mitTheos/KLORTHEOS/case/Alternate Case Design/Tenting Legs/images/choc-sofle-2.jpg

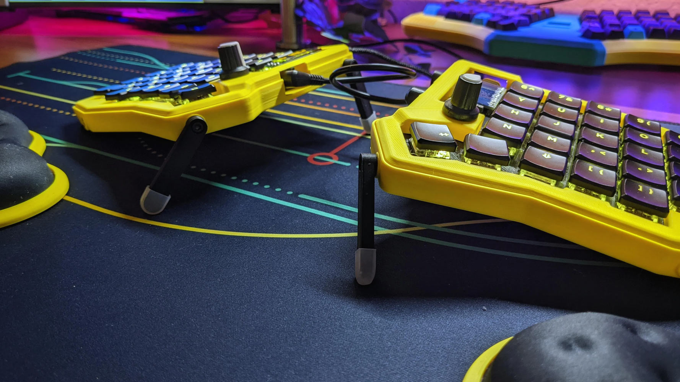
case/Alternate Case Design/Tenting Legs/images/choc-sofle-2.jpg
