mitTheos/KLORTHEOS/case/Alternate Case Design/Tenting Legs/images/tentingLeg26mm.png

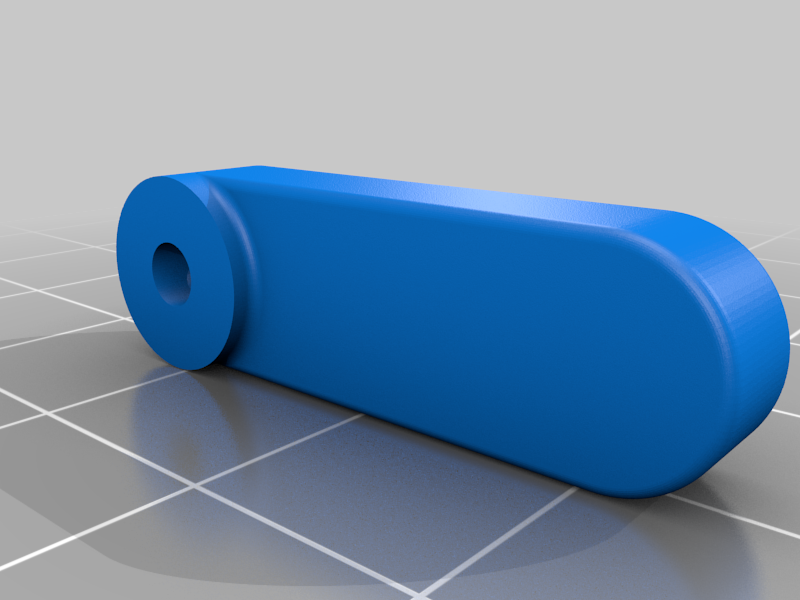
case/Alternate Case Design/Tenting Legs/images/tentingLeg26mm.png
