mitTheos/KLORTHEOS/case/Alternate Case Design/Tenting Legs/images/tentingleg36mm.png

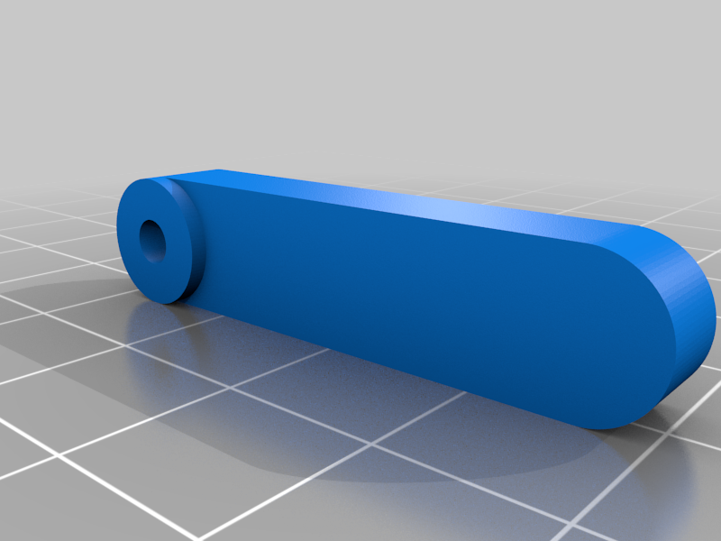
case/Alternate Case Design/Tenting Legs/images/tentingleg36mm.png
