mitTheos/KLORTHEOS/case/Alternate Case Design/Tenting Legs/images/tentingLegALT31mm.png

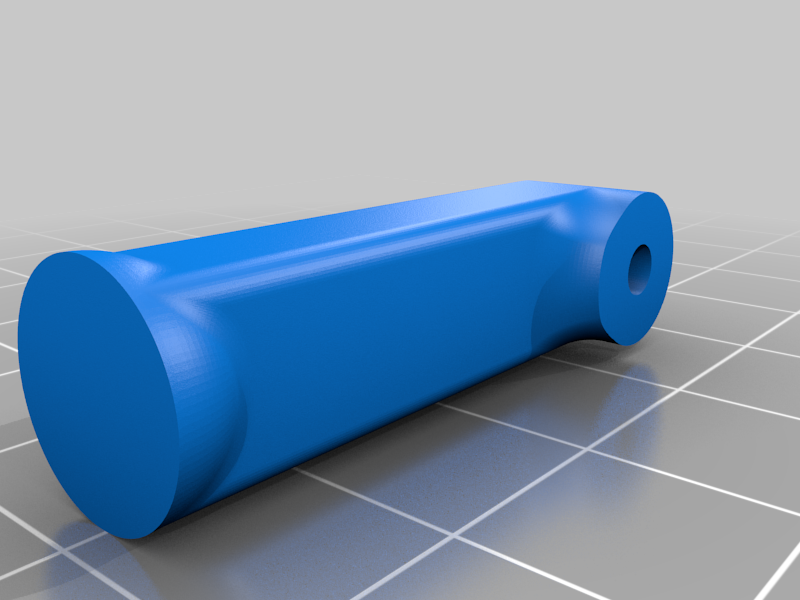
case/Alternate Case Design/Tenting Legs/images/tentingLegALT31mm.png
