mitTheos/KLORTHEOS/case/Alternate Case Design/Tenting Legs/images/tentingLegALT37mm.png

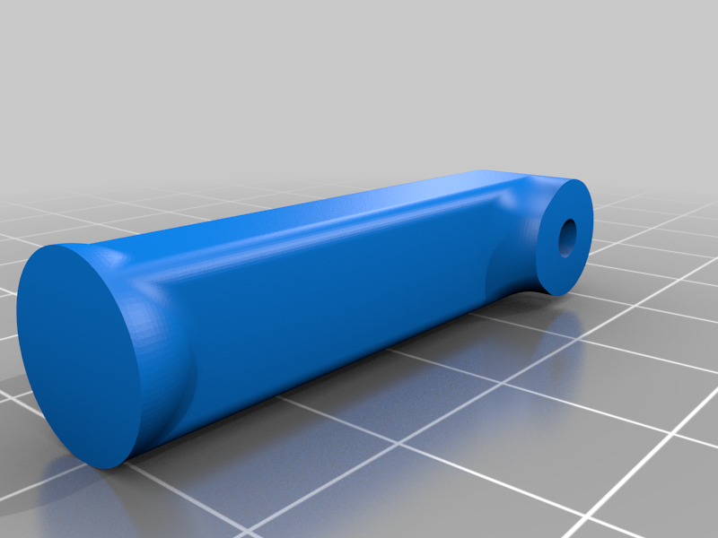
case/Alternate Case Design/Tenting Legs/images/tentingLegALT37mm.png
