mitTheos/KLORTHEOS/case/docs/images/konrad_3dp.png

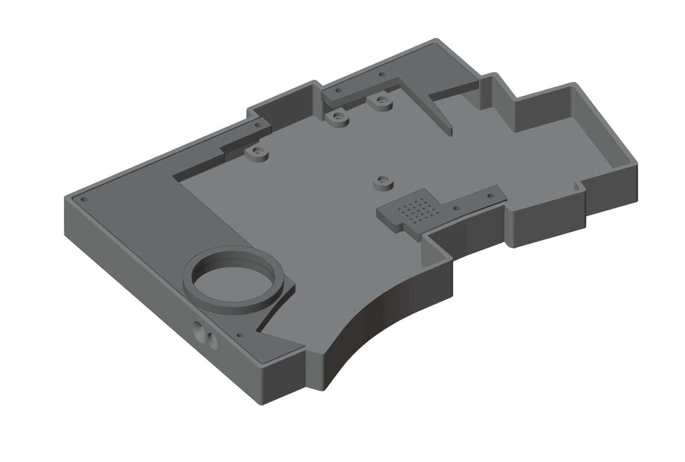
case/docs/images/konrad_3dp.png
