mitTheos/KLORTHEOS/case/docs/images/konrad_acryl.png

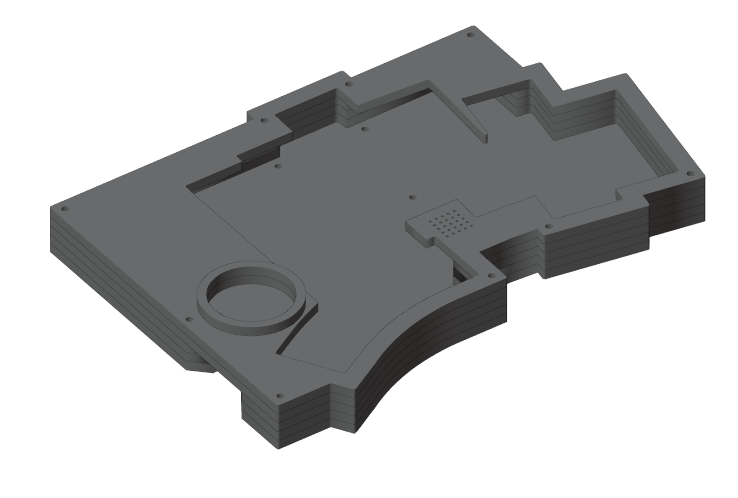
case/docs/images/konrad_acryl.png
