mitTheos/KLORTHEOS/case/docs/images/saegewerk_3dp_ble_puck.png

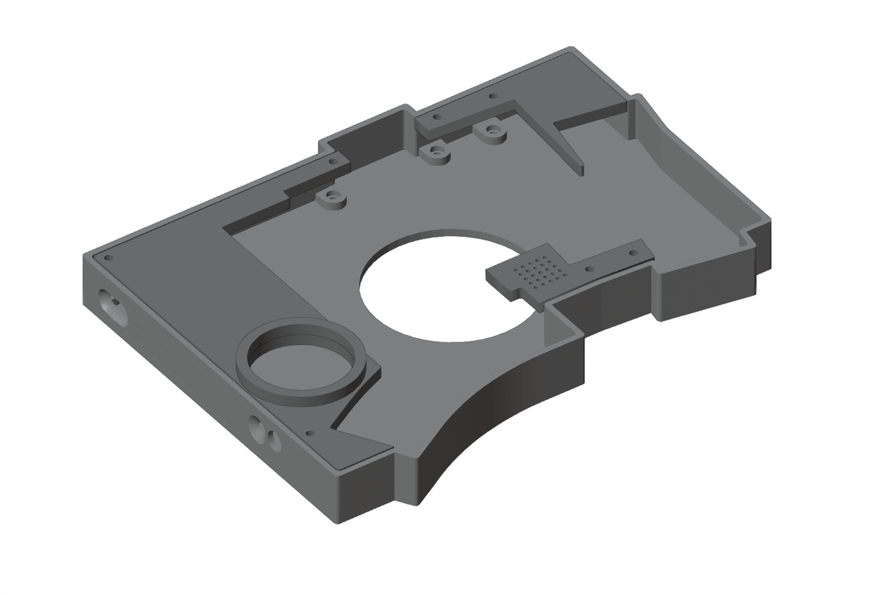
case/docs/images/saegewerk_3dp_ble_puck.png
