mitTheos/KLORTHEOS/docs/images/Klor_1.4_picture7.png

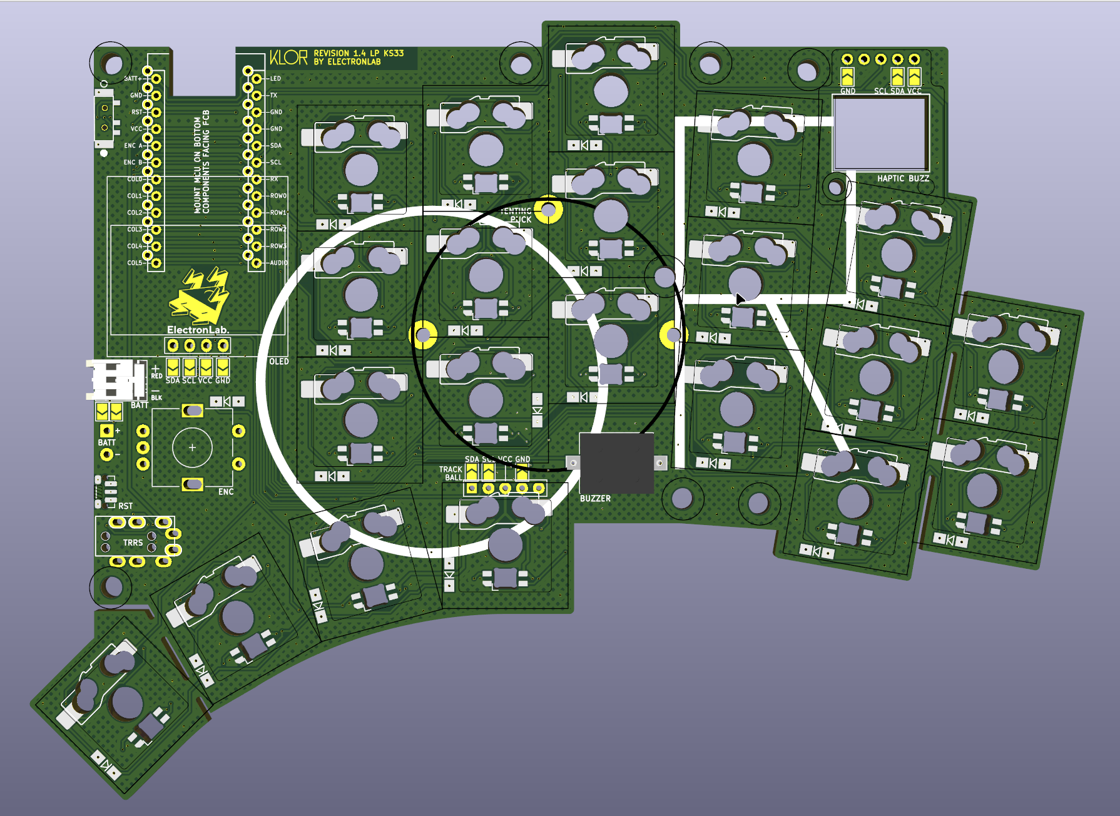
docs/images/Klor_1.4_picture7.png
