mitTheos/KLORTHEOS/docs/images/KLOR_1.5.png

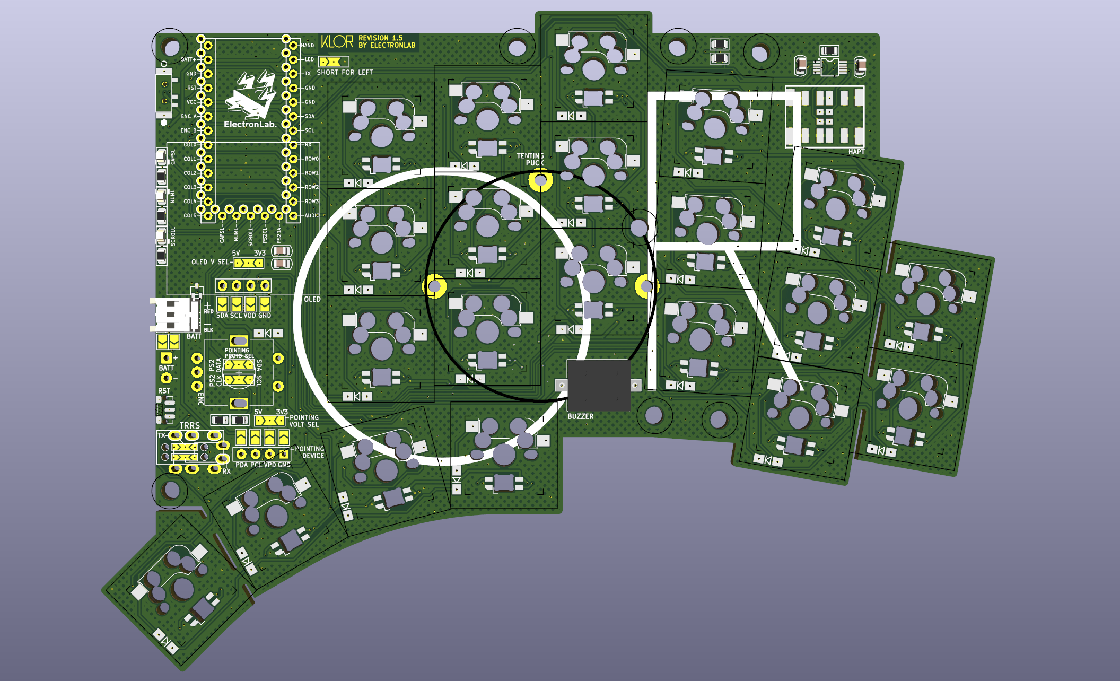
docs/images/KLOR_1.5.png
