mitTheos/KLORTHEOS/docs/images/KLOR_knob1-2.png

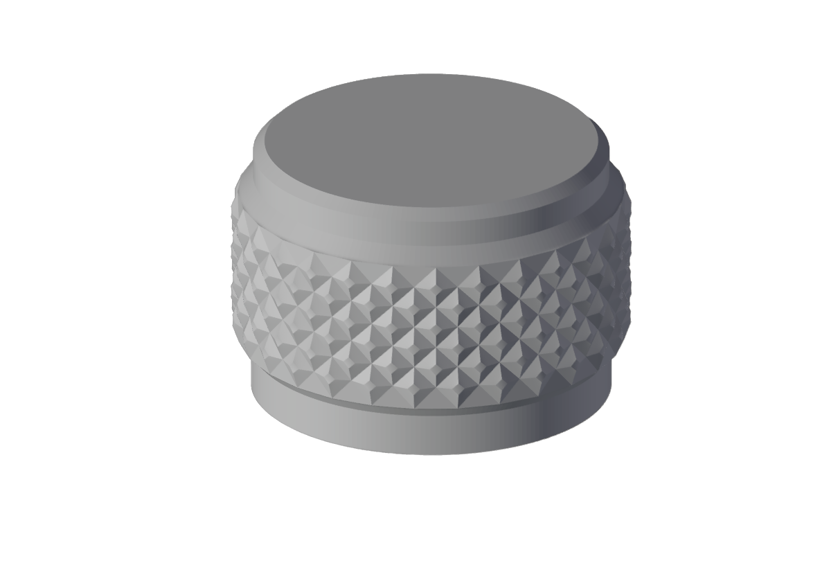
docs/images/KLOR_knob1-2.png
