mitTheos/KLORTHEOS/docs/images/KLOR_knob_resin_nylon.jpg

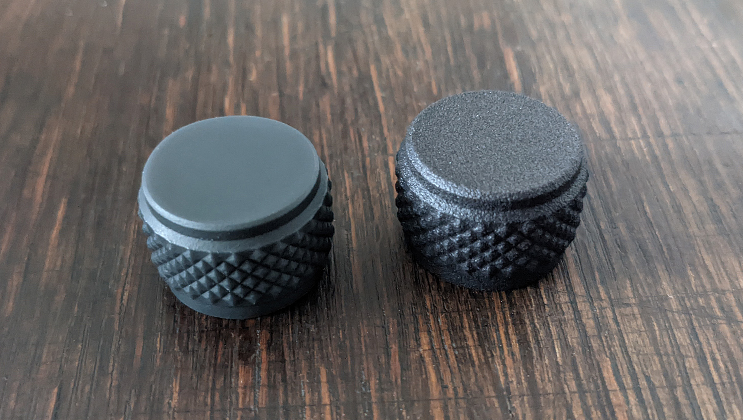
docs/images/KLOR_knob_resin_nylon.jpg
