mitTheos/KLORTHEOS/docs/images/KLOR_polydactyl_DES01.jpg

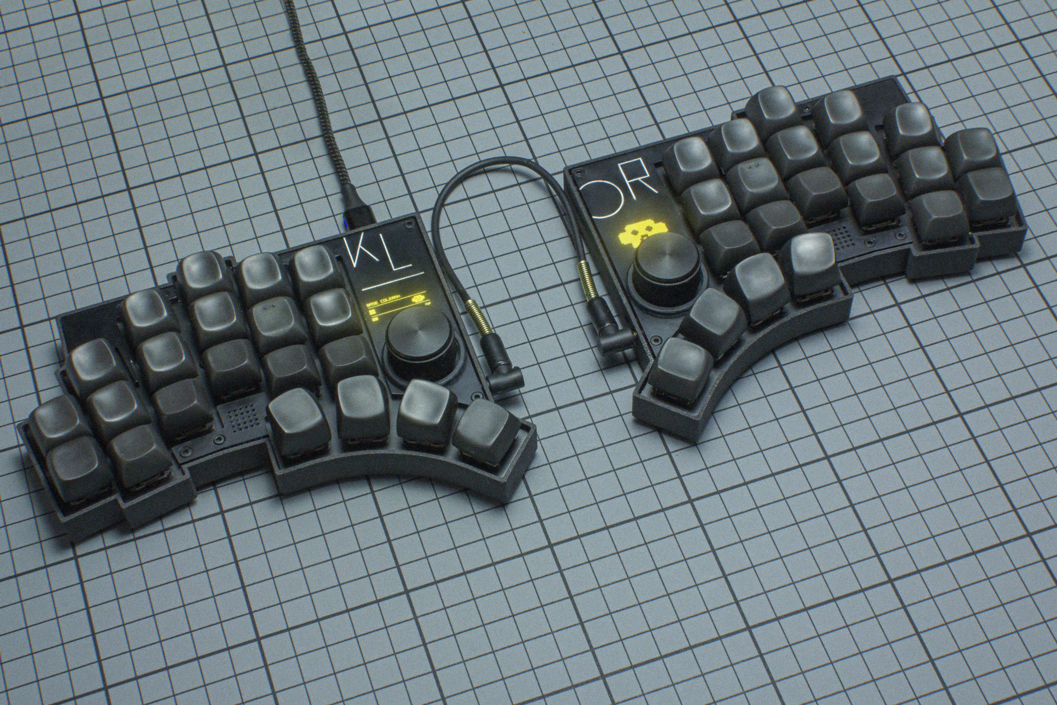
docs/images/KLOR_polydactyl_DES01.jpg
