mitTheos/KLORTHEOS/docs/images/KLOR_polydactyl_DES02.jpg

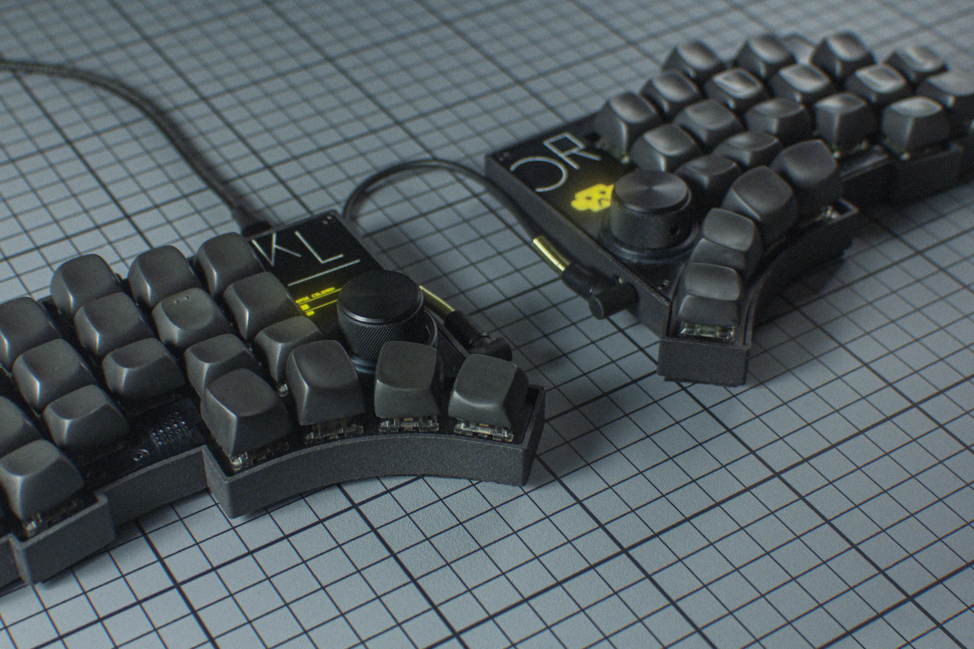
docs/images/KLOR_polydactyl_DES02.jpg
