mitTheos/KLORTHEOS/docs/images/KLOR_saegewerk_GRID01.jpg

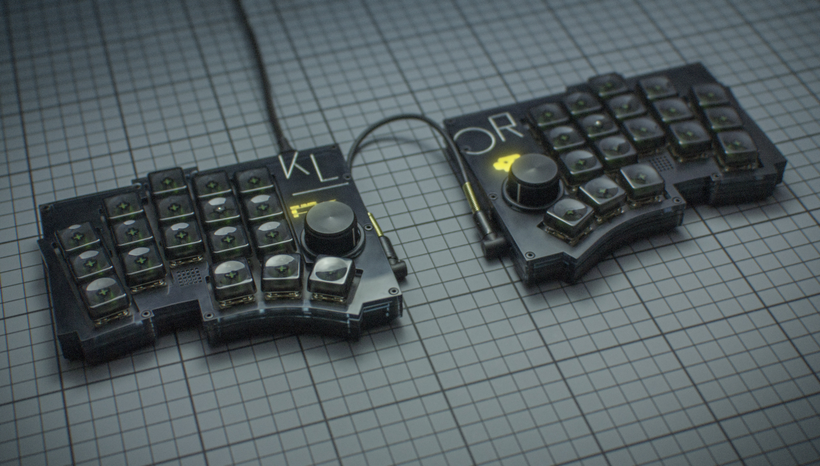
docs/images/KLOR_saegewerk_GRID01.jpg
