mitTheos/KLORTHEOS/docs/images/KLOR_saegewerk_GRID02.jpg

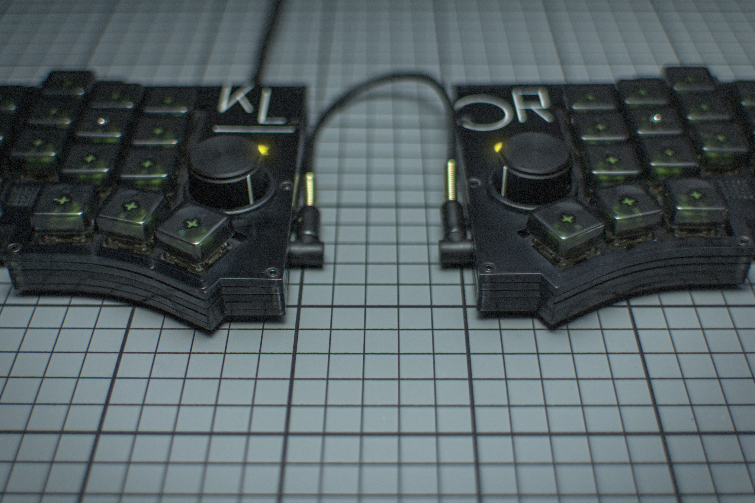
docs/images/KLOR_saegewerk_GRID02.jpg
