mitTheos/KLORTHEOS/docs/images/KLORpcb.png

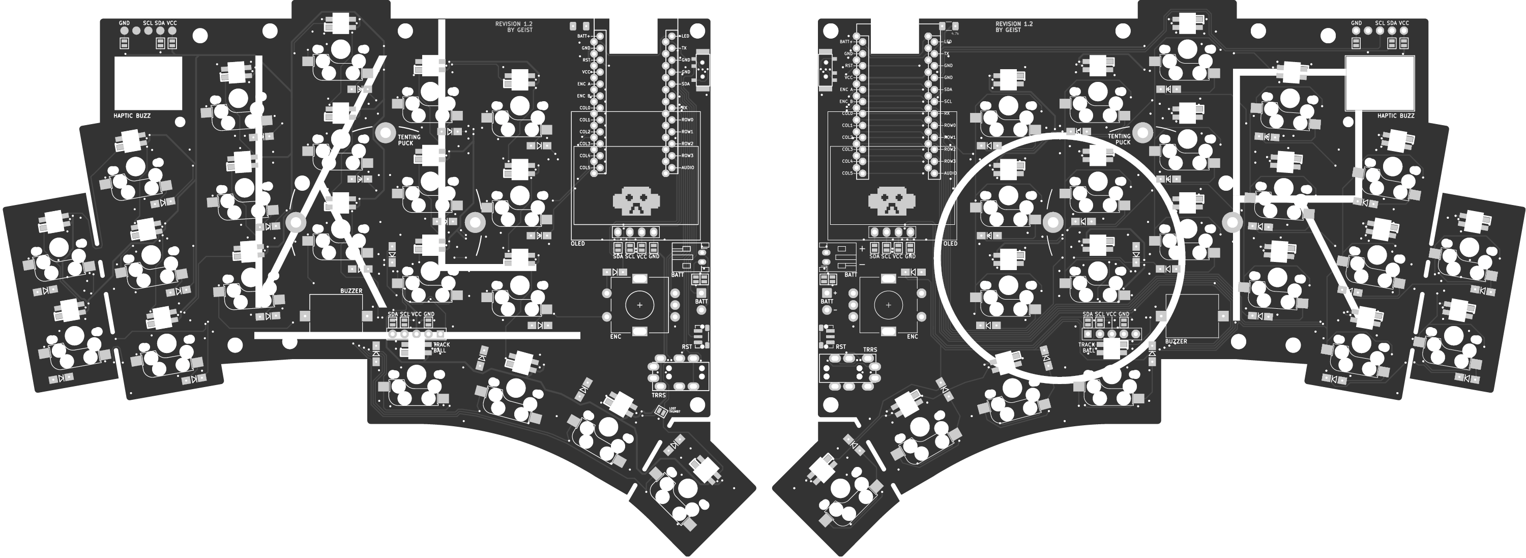
docs/images/KLORpcb.png
