mitTheos/KLORTHEOS/docs/images/KLORpinout.png

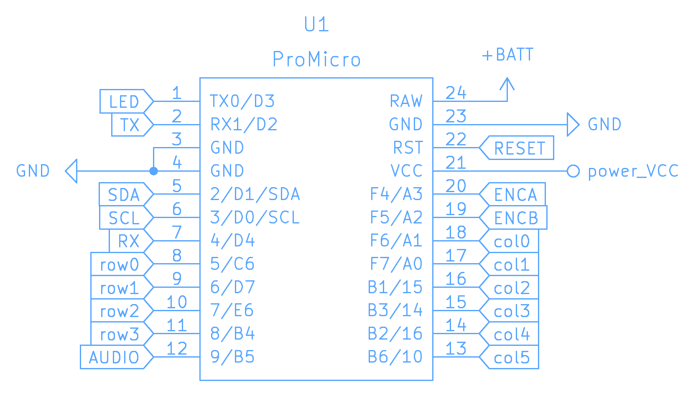
docs/images/KLORpinout.png
