mitTheos/KLORTHEOS/docs/images/KLORtraces.png

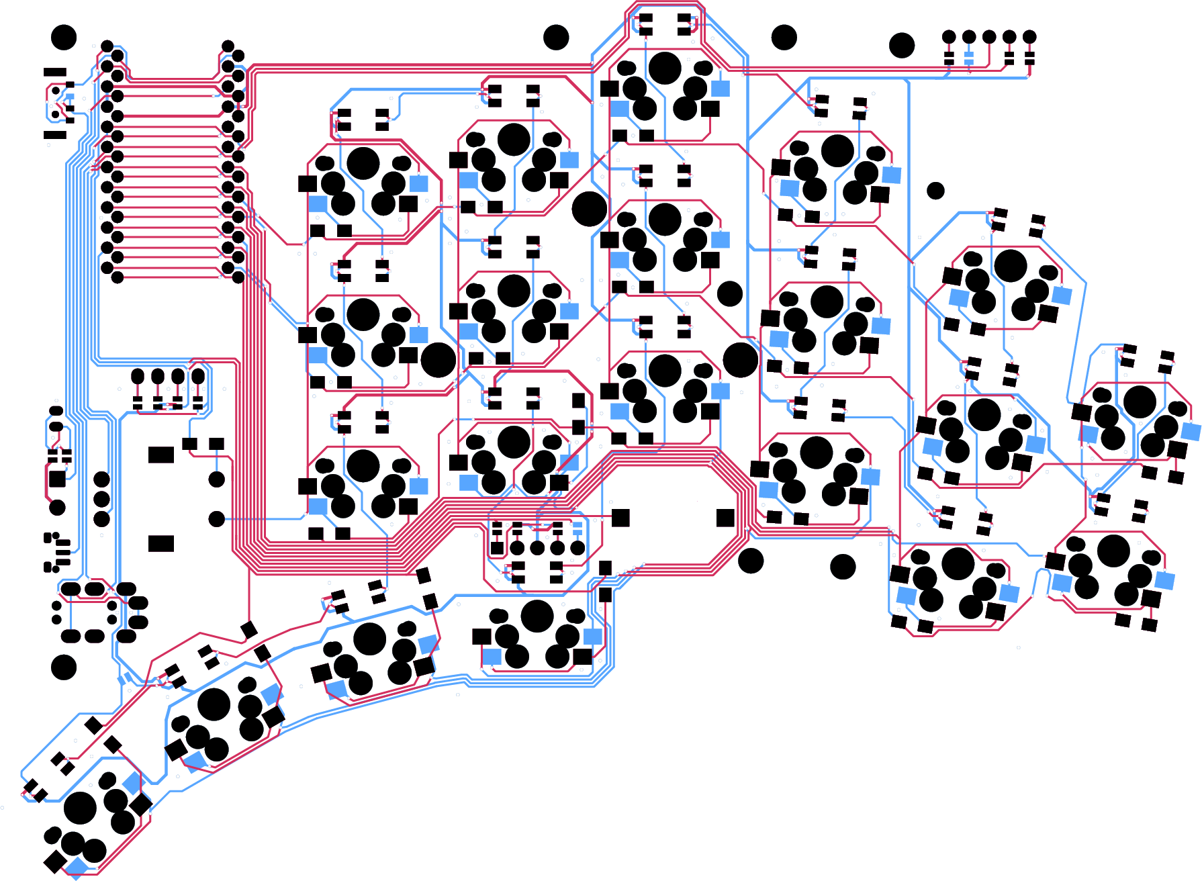
docs/images/KLORtraces.png
