mitTheos/KLORTHEOS/case/Alternate Case Design/EncoderInsert-flat-16mm.stl

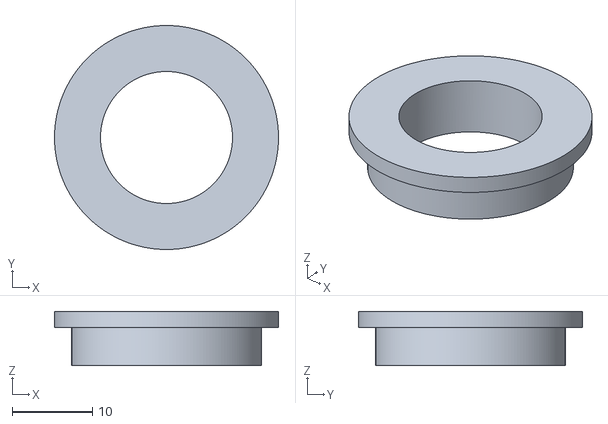
[picture p50: CAD file, 2024-07-25]
case/Alternate Case Design/EncoderInsert-flat-16mm.stl
28.0 x 28.0 x 6.80
