mitTheos/KLORTHEOS/case/Alternate Case Design/Konrad/SwitchPlate-Konrad.stl

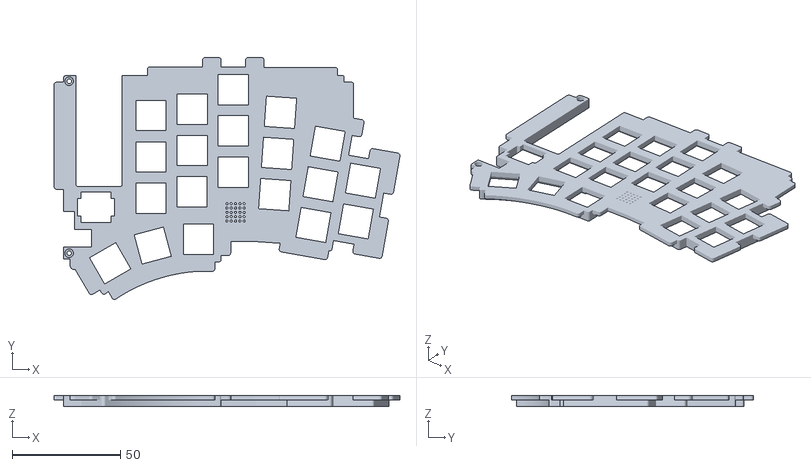
[picture p51: CAD file, 2024-07-25]
case/Alternate Case Design/Konrad/SwitchPlate-Konrad.stl
159.8 x 111.8 x 5.00
