mitTheos/KLORTHEOS/case/Alternate Case Design/Polydactyl/v2-GasketSwitchPlate.stl

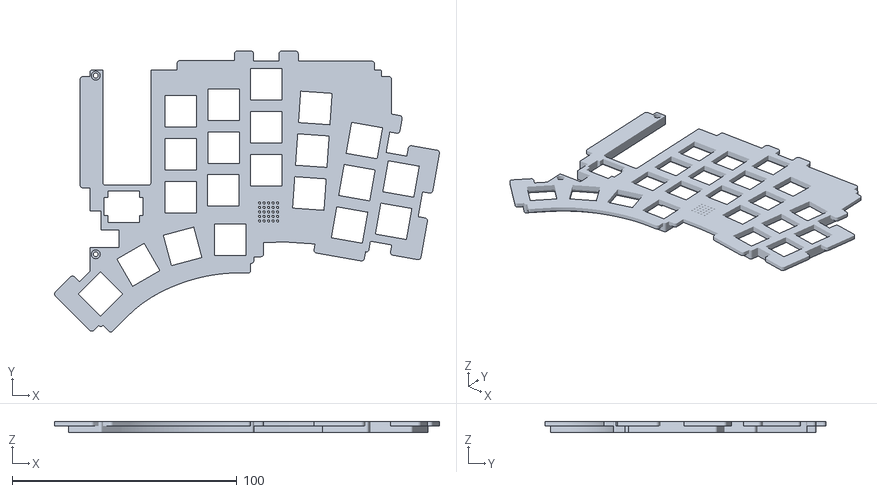
[picture p52: CAD file, 2024-07-25]
case/Alternate Case Design/Polydactyl/v2-GasketSwitchPlate.stl
171.1 x 124.9 x 5.00
