mitTheos/KLORTHEOS/case/Alternate Case Design/Saegewerk/v1-Base-Saegewerk.stl

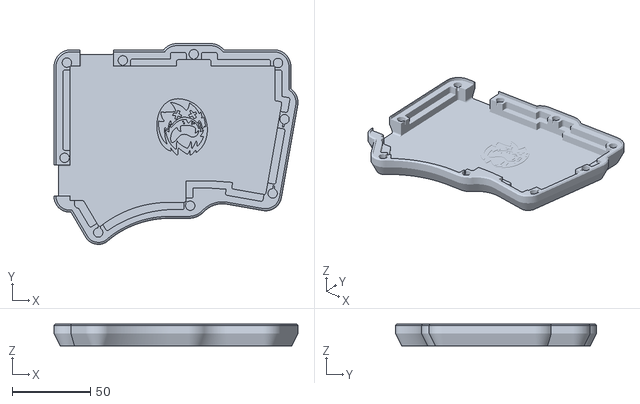
[picture p53: CAD file, 2024-07-25]
case/Alternate Case Design/Saegewerk/v1-Base-Saegewerk.stl
155.7 x 128.2 x 14.0
