mitTheos/KLORTHEOS/case/Alternate Case Design/Tenting Legs/files/tentingLeg26mm.stl

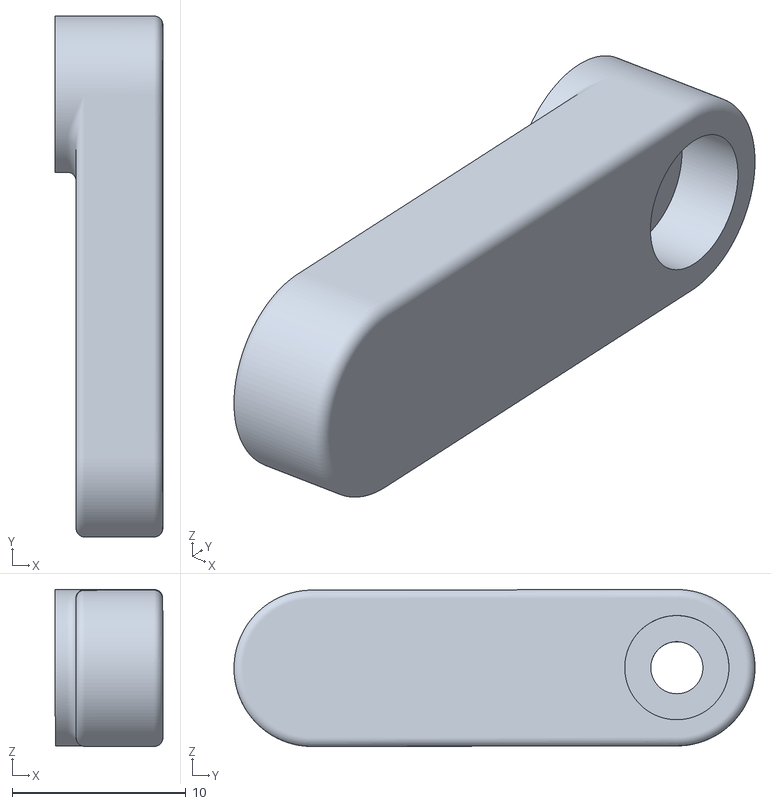
[picture p54: CAD file, 2024-08-09]
case/Alternate Case Design/Tenting Legs/files/tentingLeg26mm.stl
6.21 x 30.0 x 9.04
