mitTheos/KLORTHEOS/case/Alternate Case Design/Yubitsume/v1-BaseWithTenting-Yubitsume.stl

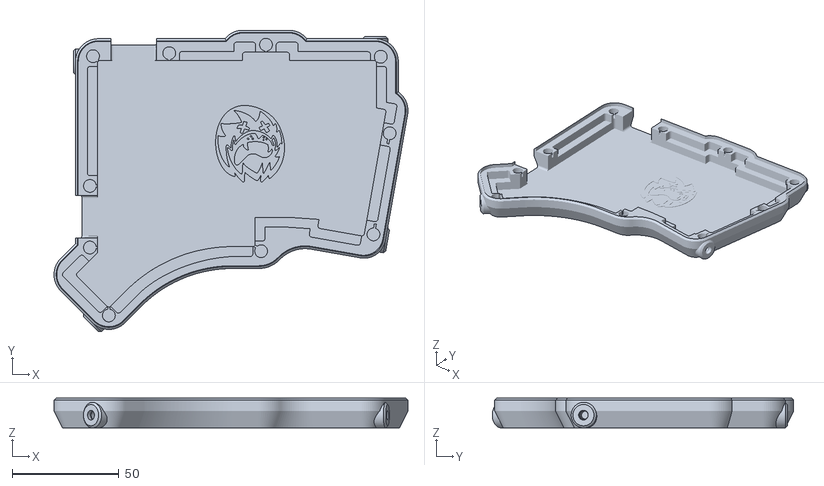
[picture p55: CAD file, 2024-07-25]
case/Alternate Case Design/Yubitsume/v1-BaseWithTenting-Yubitsume.stl
165.8 x 141.2 x 14.0
