mitTheos/KLORTHEOS/case/3DP/konrad/acrylic/KLOR_konrad_3DPcase_acrylic_logotype.dxf

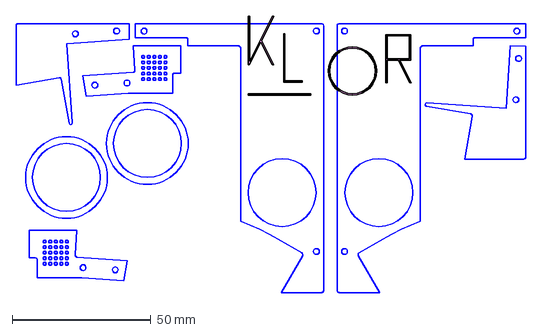
[picture p56: CAD file, 2022-08-22]
case/3DP/konrad/acrylic/KLOR_konrad_3DPcase_acrylic_logotype.dxf
183.6 x 99.5 mm
