mitTheos/KLORTHEOS/case/3DP/konrad/regular/KLOR_konrad_case_R.stl

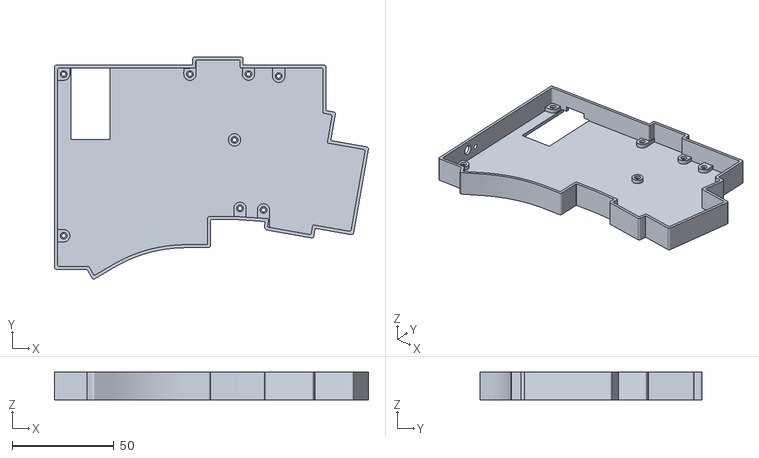
[picture p57: CAD file, 2022-09-01]
case/3DP/konrad/regular/KLOR_konrad_case_R.stl
154.3 x 109.2 x 13.6
