mitTheos/KLORTHEOS/case/Alternate Case Design/Konrad/BaseWithTenting-Konrad.stl

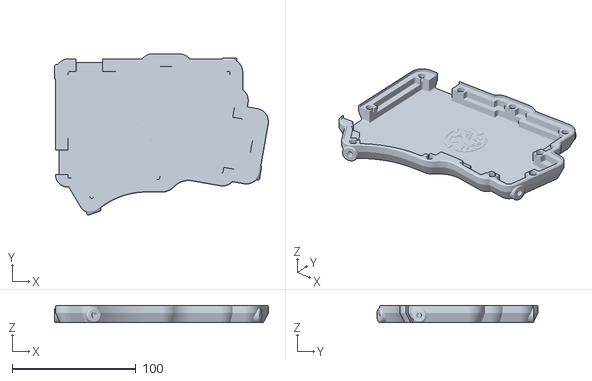
[picture p63: CAD file, 2024-07-25]
case/Alternate Case Design/Konrad/BaseWithTenting-Konrad.stl
172.8 x 130.1 x 14.0
