mitTheos/KLORTHEOS/case/Alternate Case Design/Polydactyl/v2-GasketBase.stl

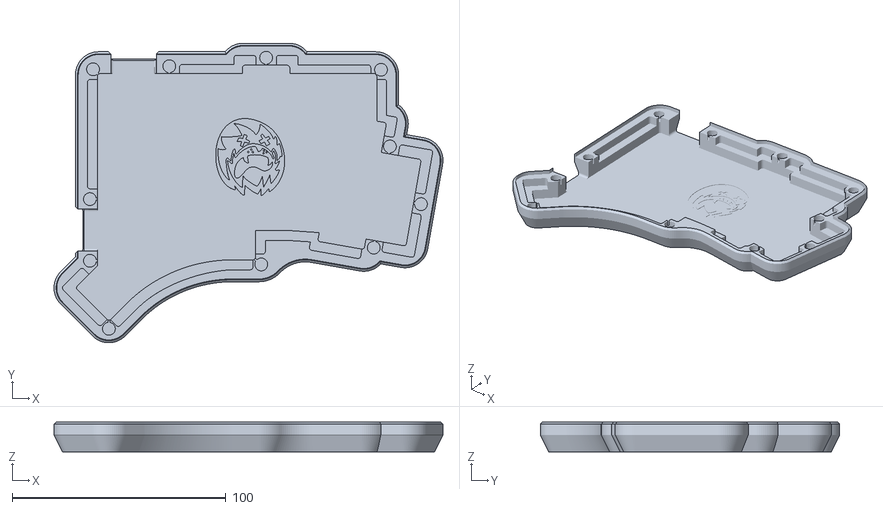
[picture p64: CAD file, 2024-07-25]
case/Alternate Case Design/Polydactyl/v2-GasketBase.stl
182.0 x 140.1 x 14.0
