mitTheos/KLORTHEOS/case/Alternate Case Design/Saegewerk/v1-SwitchPlate-Saegewerk.stl

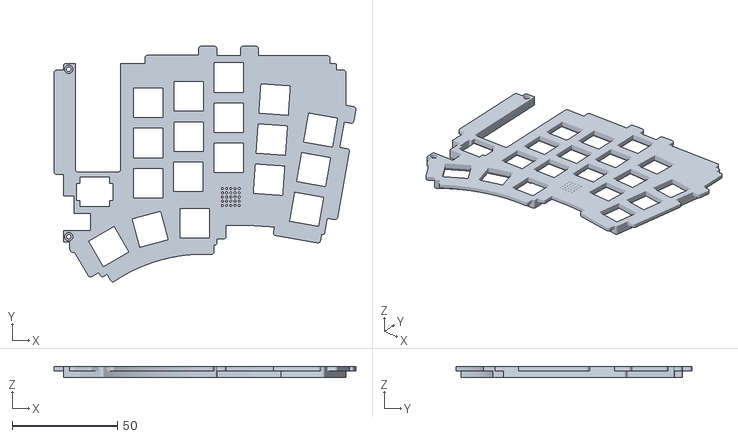
[picture p65: CAD file, 2024-07-25]
case/Alternate Case Design/Saegewerk/v1-SwitchPlate-Saegewerk.stl
143.2 x 111.8 x 5.00
