mitTheos/KLORTHEOS/case/Alternate Case Design/Tenting Legs/files/tentingLeg42mm.stl

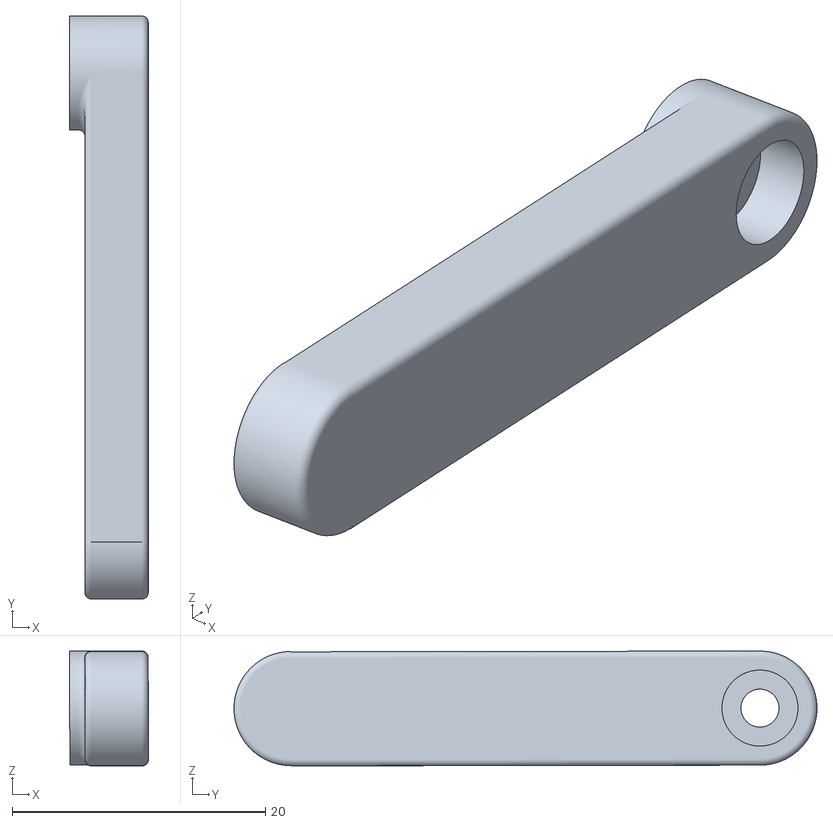
[picture p66: CAD file, 2024-08-09]
case/Alternate Case Design/Tenting Legs/files/tentingLeg42mm.stl
6.21 x 46.0 x 9.07
