mitTheos/KLORTHEOS/case/Alternate Case Design/Yubitsume/v1-SwitchPlate-Yubitsume.stl

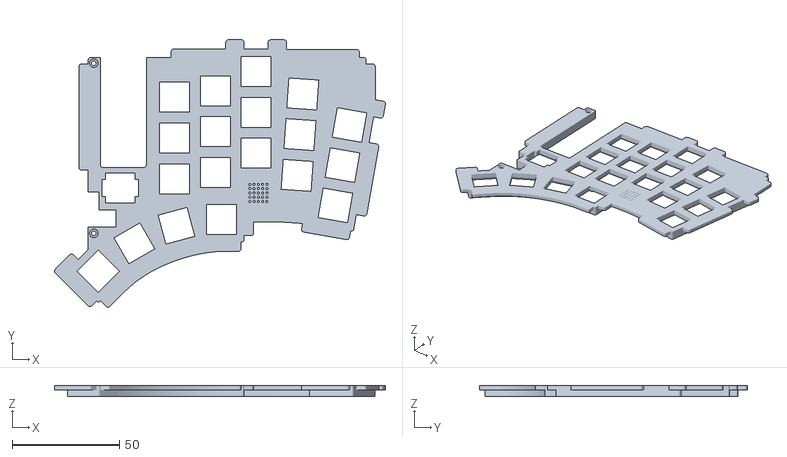
[picture p67: CAD file, 2024-07-25]
case/Alternate Case Design/Yubitsume/v1-SwitchPlate-Yubitsume.stl
154.6 x 124.9 x 5.00
