mitTheos/KLORTHEOS/case/3DP/saegewerk/bluetooth/KLOR_saegewerk_case_ble_R.stl

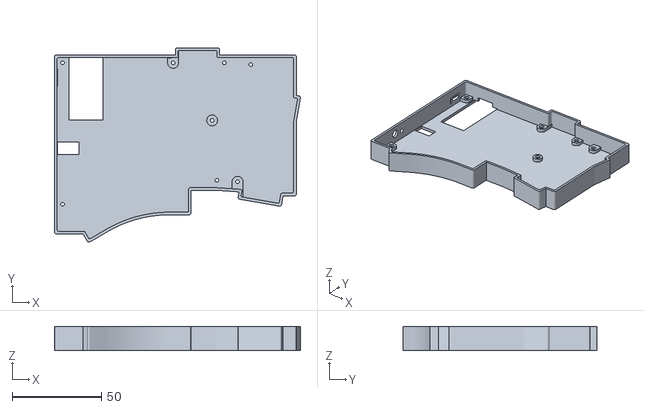
[picture p68: CAD file, 2022-09-01]
case/3DP/saegewerk/bluetooth/KLOR_saegewerk_case_ble_R.stl
138.1 x 109.2 x 13.6
