mitTheos/KLORTHEOS/case/Alternate Case Design/EncoderInsert-16mm.stl

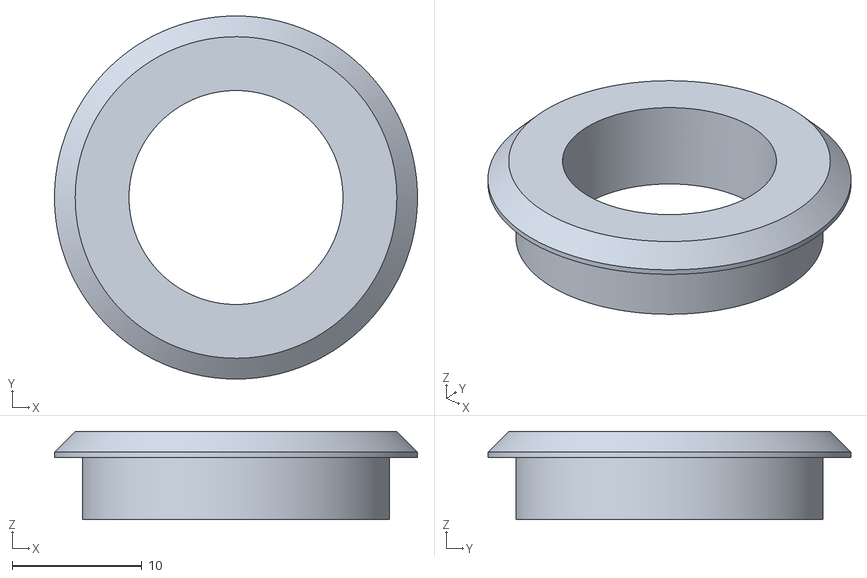
[picture p69: CAD file, 2024-07-25]
case/Alternate Case Design/EncoderInsert-16mm.stl
28.0 x 28.0 x 6.80
