mitTheos/KLORTHEOS/case/Alternate Case Design/Polydactyl/v2-GasketBaseWithTenting.stl

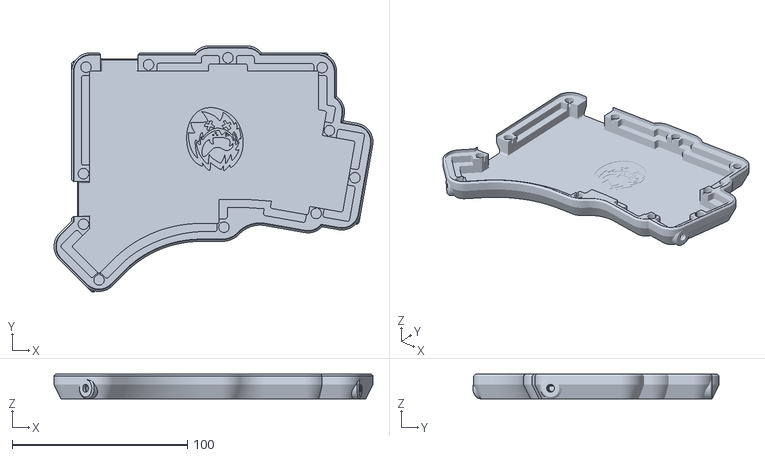
[picture p70: CAD file, 2024-07-25]
case/Alternate Case Design/Polydactyl/v2-GasketBaseWithTenting.stl
182.0 x 140.5 x 14.0
