mitTheos/KLORTHEOS/case/Alternate Case Design/EncoderInsert.stl

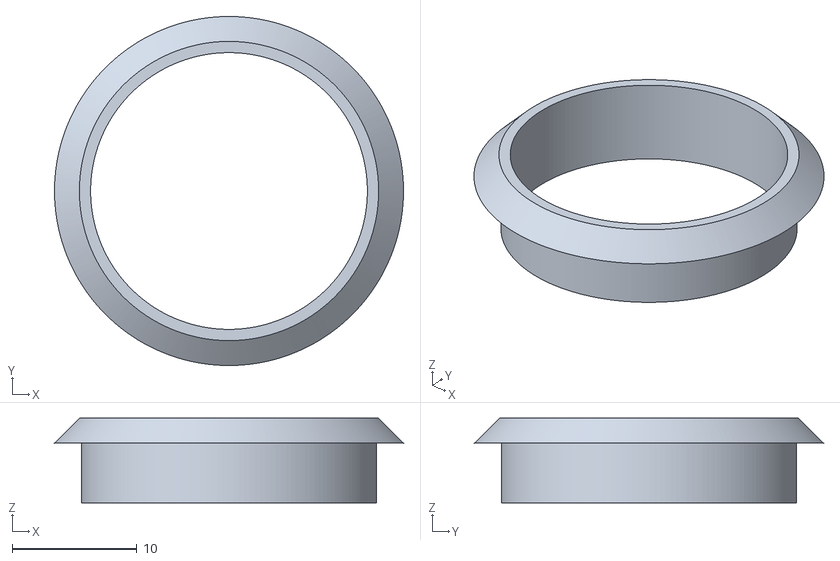
[picture p73: CAD file, 2024-07-25]
case/Alternate Case Design/EncoderInsert.stl
28.0 x 28.0 x 6.80
