mitTheos/KLORTHEOS/case/Alternate Case Design/Tenting Legs/files/tentingLegALT37mm.stl

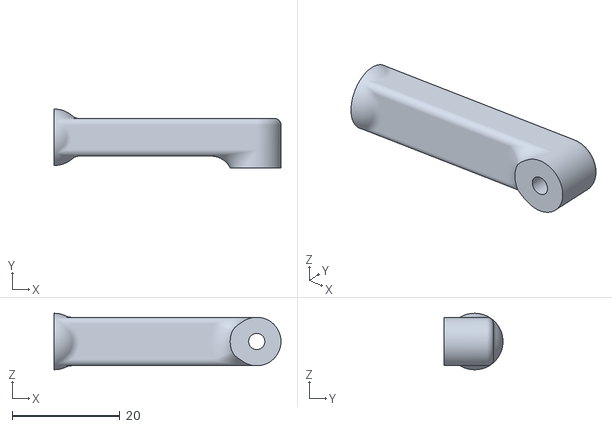
[picture p74: CAD file, 2024-08-09]
case/Alternate Case Design/Tenting Legs/files/tentingLegALT37mm.stl
42.1 x 10.9 x 10.5
