mitTheos/KLORTHEOS/case/Alternate Case Design/Tenting Legs/files/TentingLeg38mm.stl

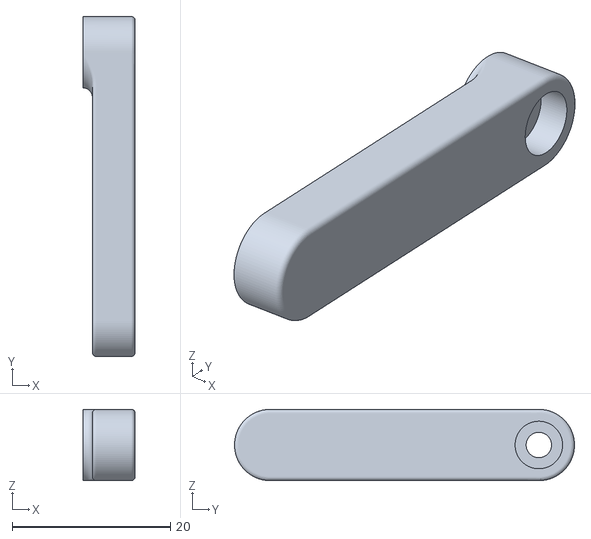
[picture p75: CAD file, 2024-08-09]
case/Alternate Case Design/Tenting Legs/files/TentingLeg38mm.stl
6.60 x 42.9 x 9.00
