mitTheos/KLORTHEOS/case/Alternate Case Design/Yubitsume/v1-Base-Yubitmsume.stl

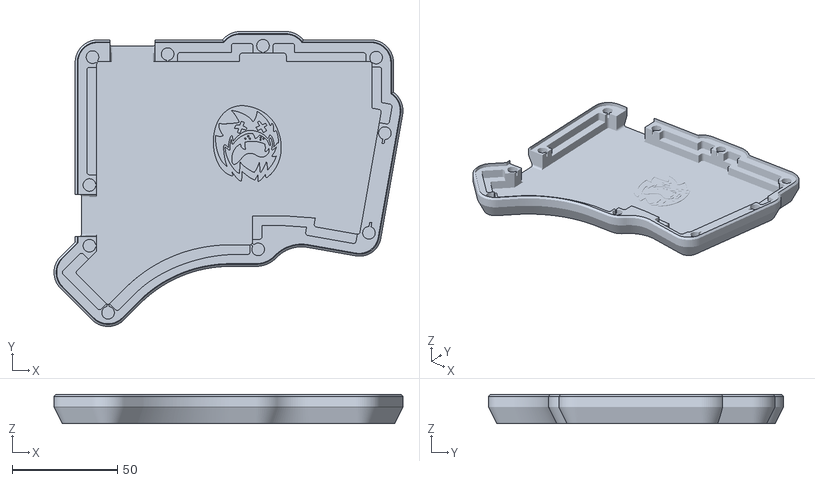
[picture p76: CAD file, 2024-07-25]
case/Alternate Case Design/Yubitsume/v1-Base-Yubitmsume.stl
165.8 x 140.1 x 14.0
