mitTheos/KLORTHEOS/case/Alternate Case Design/Tenting Legs/files/tentingLegALT31mm.stl

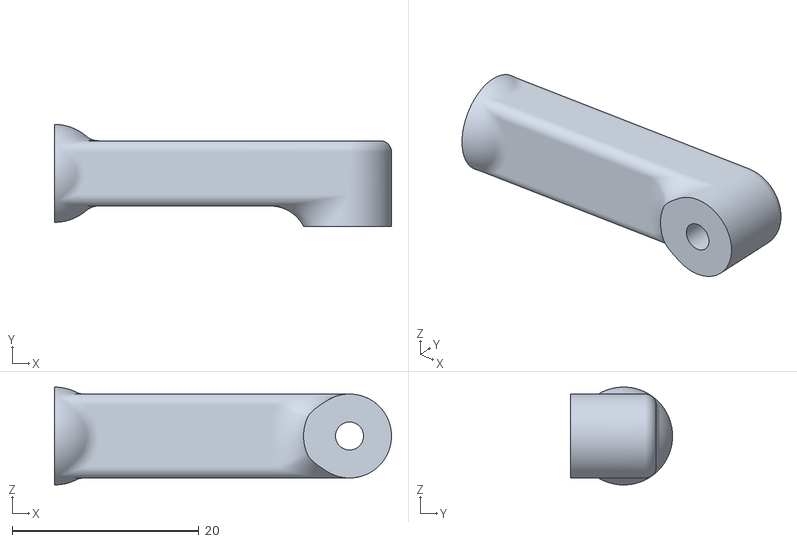
[picture p78: CAD file, 2024-08-09]
case/Alternate Case Design/Tenting Legs/files/tentingLegALT31mm.stl
36.1 x 10.9 x 10.5
